ko6lvm/RPCRC/img/cad_case.png

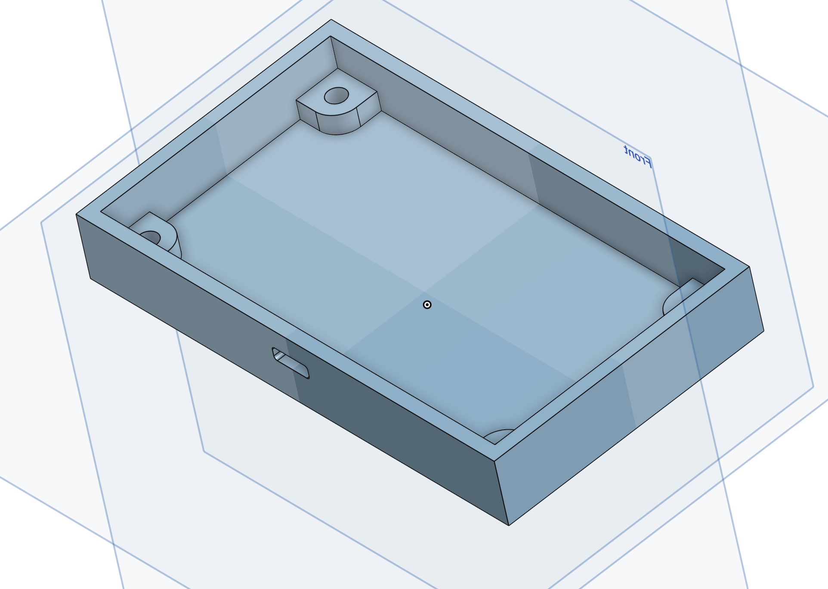
img/cad_case.png
