ko6lvm/RPCRC/img/cad_lid.png

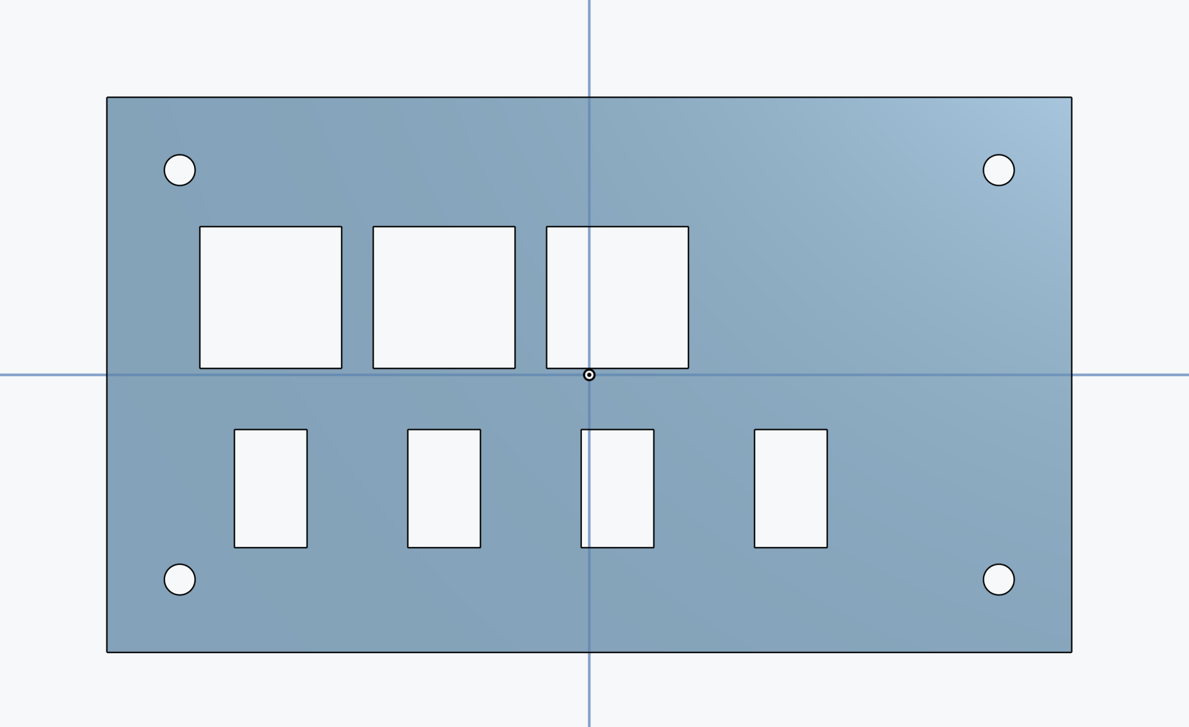
img/cad_lid.png
