ko6lvm/RPCRC/img/cover_close.png

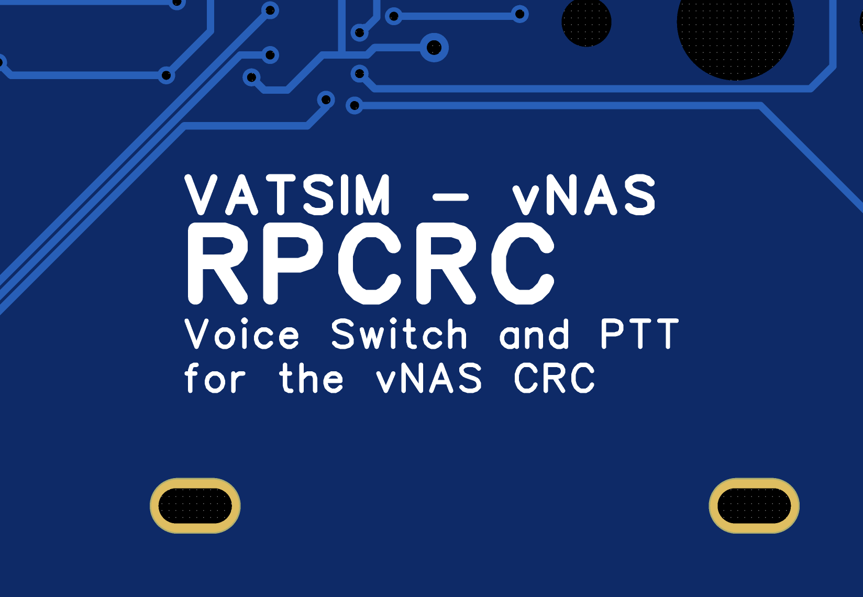
img/cover_close.png
