ko6lvm/RPCRC/img/pcb_3d_model_side.png

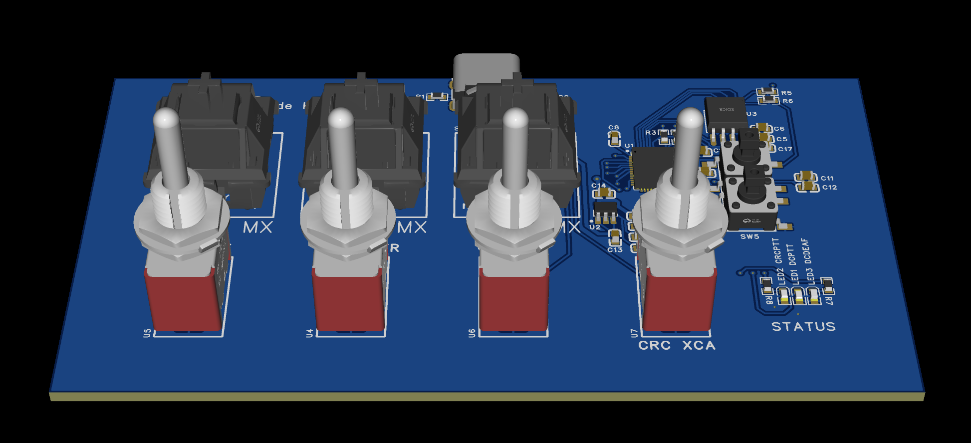
img/pcb_3d_model_side.png
