ko6lvm/RPCRC/img/pcb_editor_view.png

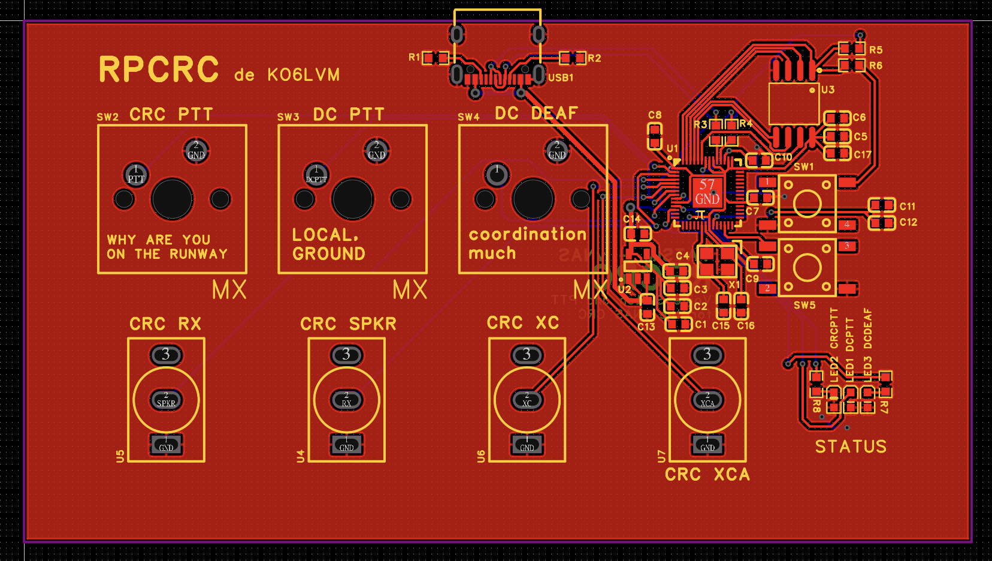
img/pcb_editor_view.png
