ko6lvm/RPCRC/img/assembly_angle_right.png

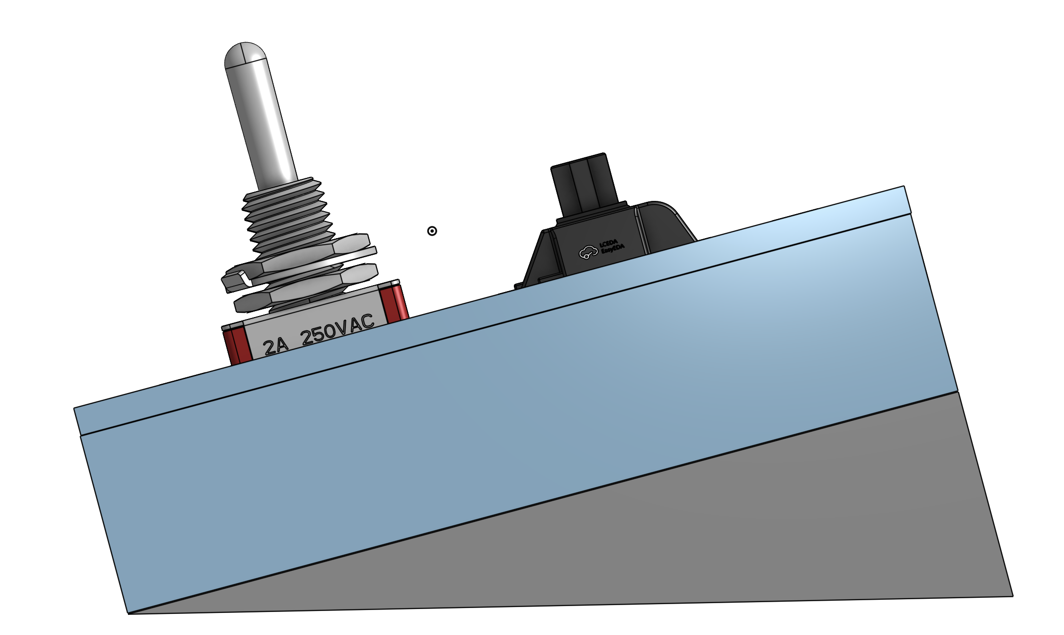
img/assembly_angle_right.png
