ko6lvm/RPCRC/img/assembly_angle_side.png

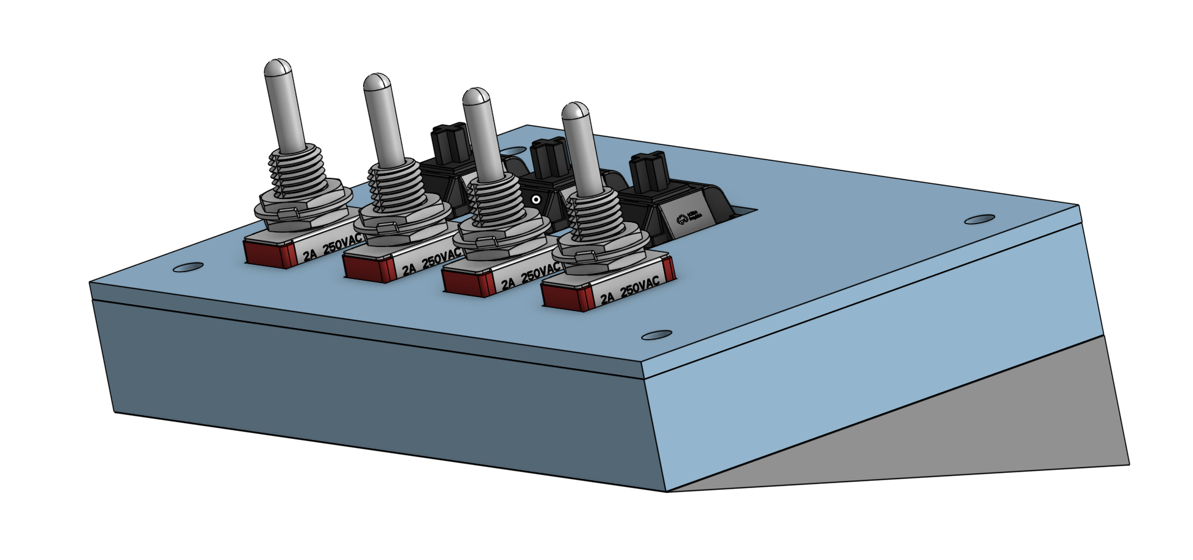
img/assembly_angle_side.png
