ko6lvm/RPCRC/img/assembly_left.png

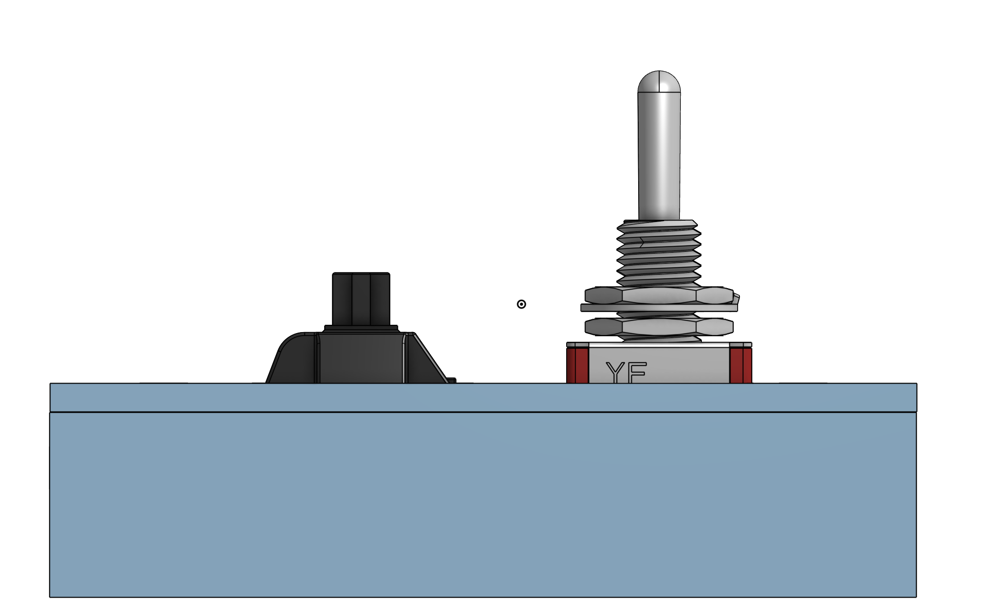
img/assembly_left.png
