ko6lvm/RPCRC/img/assembly_side_angle.png

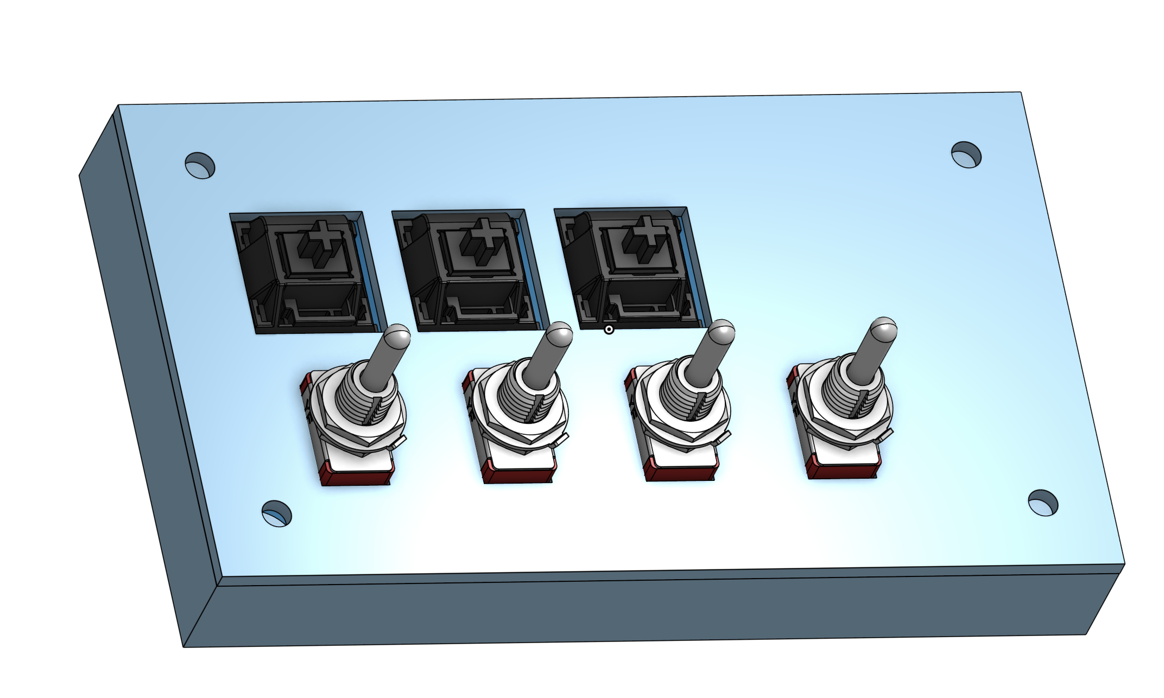
img/assembly_side_angle.png
